kiu/BaSHi/BaSHi-SM-1/REV_A/BaSHi-SM-1-render_bottom.png

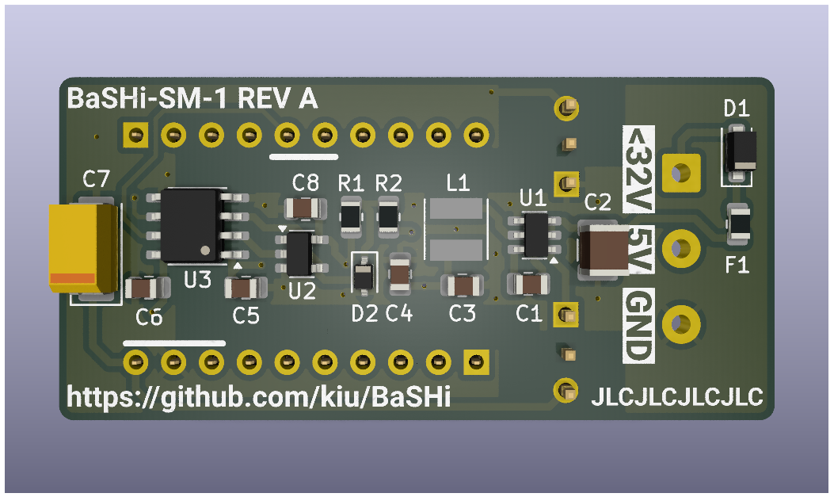
BaSHi-SM-1/REV_A/BaSHi-SM-1-render_bottom.png
